Archive-663/nishiKodak/Nikon F DX/README.md

## Lot no. 006 | NishiKodak - for Nikon F DX

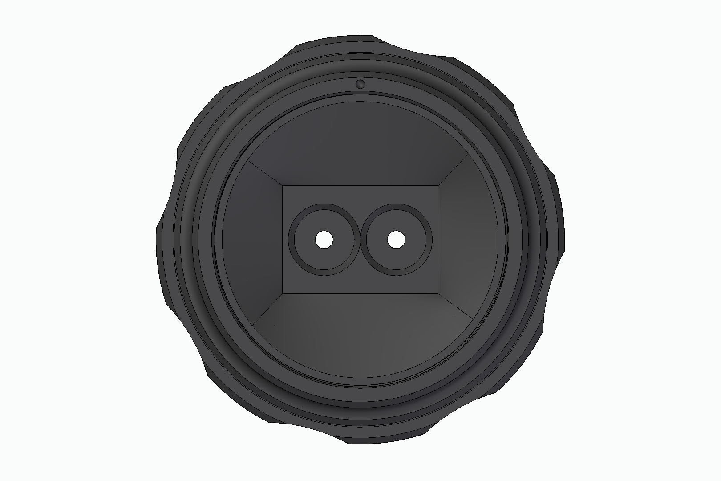
[picture p33: ASSETS/nishiKodak_nikonF_DX.jpg]

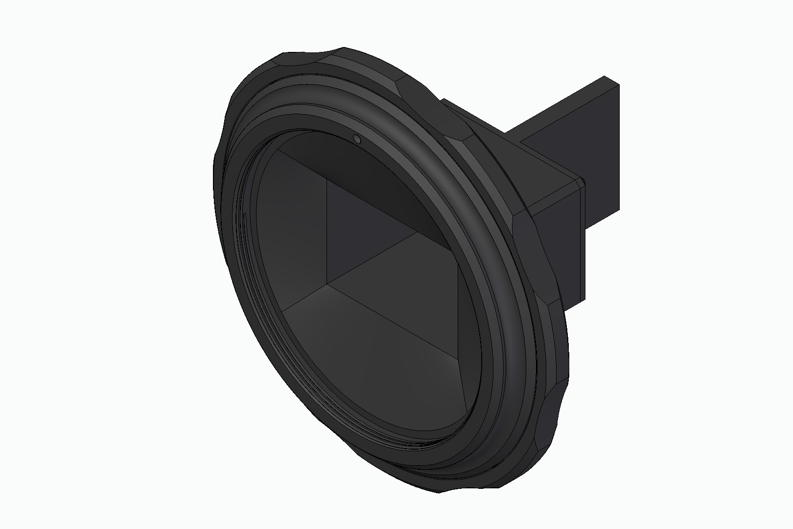
[picture p34: ASSETS/nishiKodak_nikonF_DX-1.jpg]

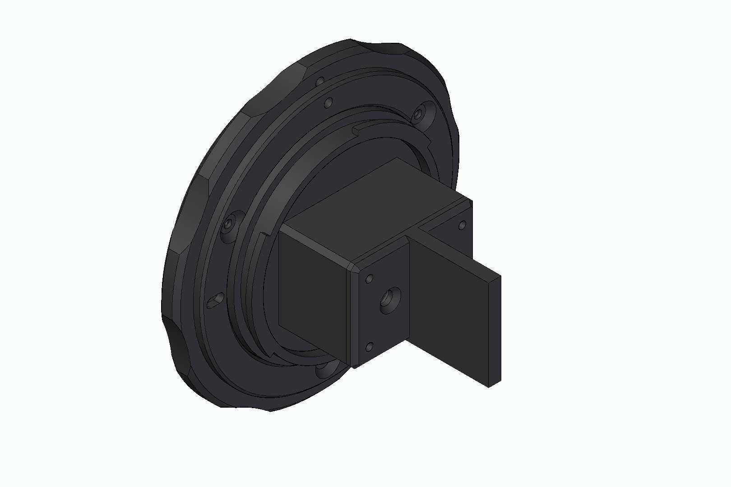
[picture p35: ASSETS/nishiKodak_nikonF_DX-2.jpg]


### Features:
- Breech-lock  mounting ring
- 30mm focal length
- Fixed ~f11 aperture
- Two individual images on one frame

### Compatibility Note:
You need a Nikon body that allows for mirror lock up. Some older film cameras allowed you to hold the mirror up with hardware, but there are some that link the mirror actuation to the shutter actuation so you can't lock your mirror up. Just make sure you have mirror lock up. Tested on a D700 + D200.

### What you'll need:
- Lots of M1.6 x 5mm pan head screws (PETG or ABS filament)
  
  or

- Lots of M1.6 x 5mm self tapping screws (ABS filament)
- 1x M1.6 tap
- 2x Kodak Funsaver lenses (post-2015 expiration date. Kodak had a few lens changes in the Funsaver production lifetime. You'll need a recent Funsaver to make this work)
- <a href="https://github.com/Archive-663/kodakFunsaver/tree/main/DSLRviewFinder/STL">30mm Kodak Funsaver Viewfinder Rehousing</a>

### What would be helpful:
- M1.4 drill bit
- M1.8/M2 drill bit

### Printing help:
I print with PETG because it's pretty easy to set up with and dial in. If you want to use something else, go for it. I'd stay away from PLA because it's not the best in heat and against solvents. 

Generally, my designs have chamfers on the print face of the STL.

Please view the printOrientation.3mf file for help with orienting the parts on the printer bed. 

### Assembly help:
I suggest drilling holds to their correct tap size before tapping. The M1.6 holes should be drilled out to 1.4mm then tapped with the M1.6 tap. 

When assembling the rotating assemblies use some synthetic grease similar to Super Lube PTFE or keycap lube to make the rotate function smoother.

Please view the _assembly.stp file for help in parts orientation. If you do not have a CAD program, <a href="https://www.freecad.org/downloads.php" target="_blank">download FreeCAD</a> to view the assembly file and better understand how it should assemble.

### Samples:

Coming Soon.

### Helpful videos:
- <a href="https://www.youtube.com/watch?v=ZdX-1SL8kYE" target="_blank">Old Print and Assembly Video</a>
- <a href="https://www.youtube.com/watch?v=JzHJL4l5Iv4" target="_blank">How to wigglegram</a>
- <a href="https://www.youtube.com/watch?v=mniP1P2PrpM" target="_blank">Kodak Funsaver Disassembly</a>

### Help support Archive 663 with a dontation or monthly sub
