Archive-663/nishiKodak/Sony E/STL/nishiKodak_sonyE_depthChecker.stl

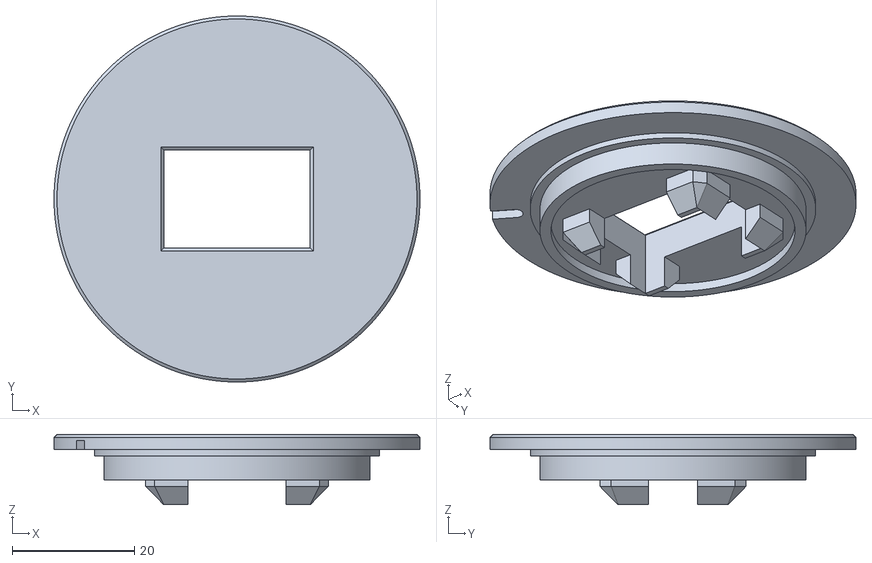
[picture p57: CAD file, 2023-11-09]
Sony E/STL/nishiKodak_sonyE_depthChecker.stl
60.0 x 60.0 x 11.5
