Archive-663/nishiKodak/Sony FE/STL/nishiKodak_sonyFE_depthChecker.stl

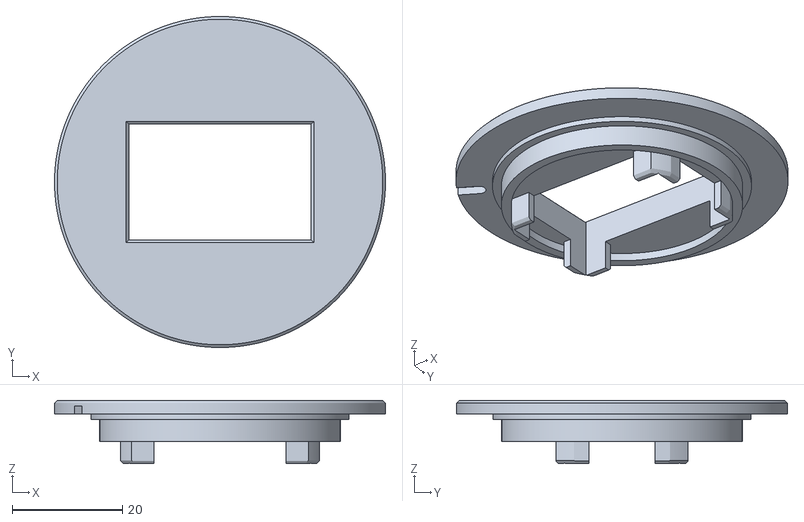
[picture p58: CAD file, 2023-11-09]
Sony FE/STL/nishiKodak_sonyFE_depthChecker.stl
60.0 x 60.0 x 11.5
