Archive-663/nishiKodak/Canon EF-S/STL/nishiKodak_canonEF_rearCap.stl

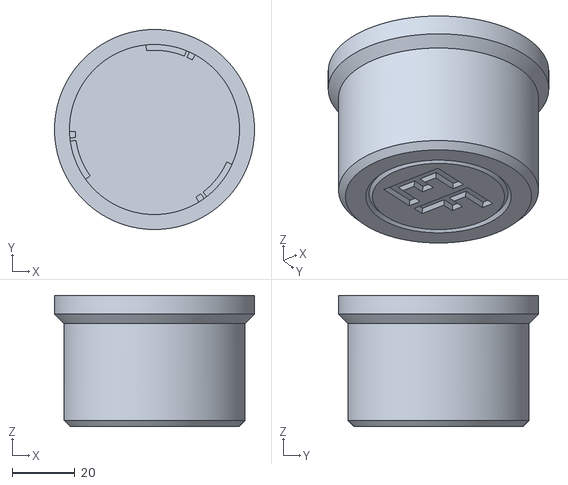
[picture p59: CAD file, 2023-11-06]
Canon EF-S/STL/nishiKodak_canonEF_rearCap.stl
64.0 x 64.0 x 42.0
