Archive-663/nishiKodak/Canon EF/STL/nishiKodak_canonEF_mountLockRing.stl

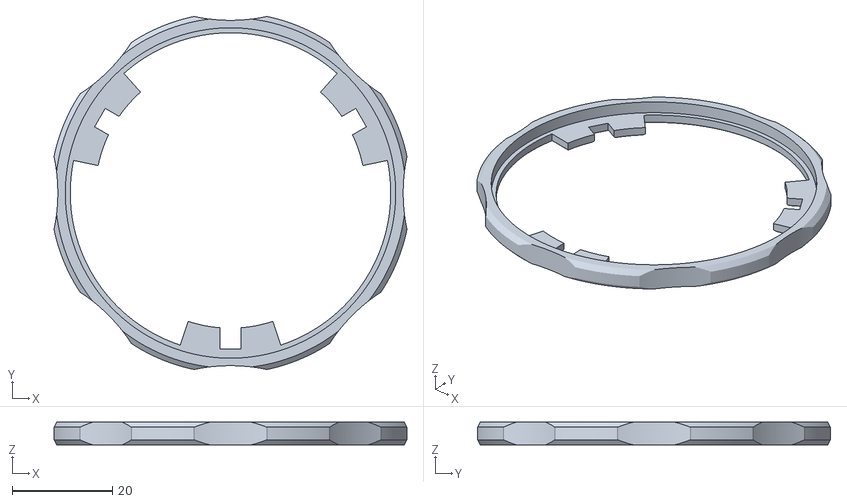
[picture p60: CAD file, 2023-11-06]
Canon EF/STL/nishiKodak_canonEF_mountLockRing.stl
70.5 x 70.5 x 4.50
