Archive-663/nishiKodak/Canon FD/STL/nishiKodak_canonFD_breechLock.stl

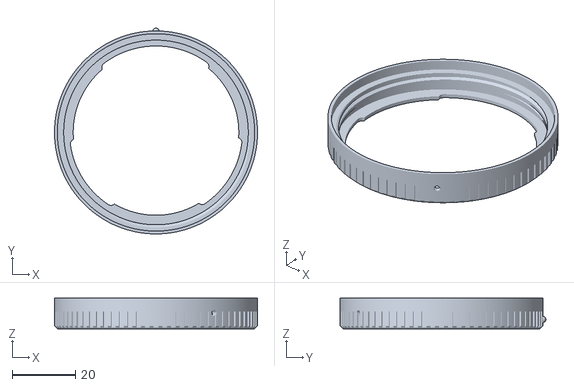
[picture p61: CAD file, 2023-11-06]
Canon FD/STL/nishiKodak_canonFD_breechLock.stl
64.0 x 64.9 x 9.75
