Archive-663/nishiKodak/Canon RF/STL/printOrientation_nishiKodak_canonRF.3mf

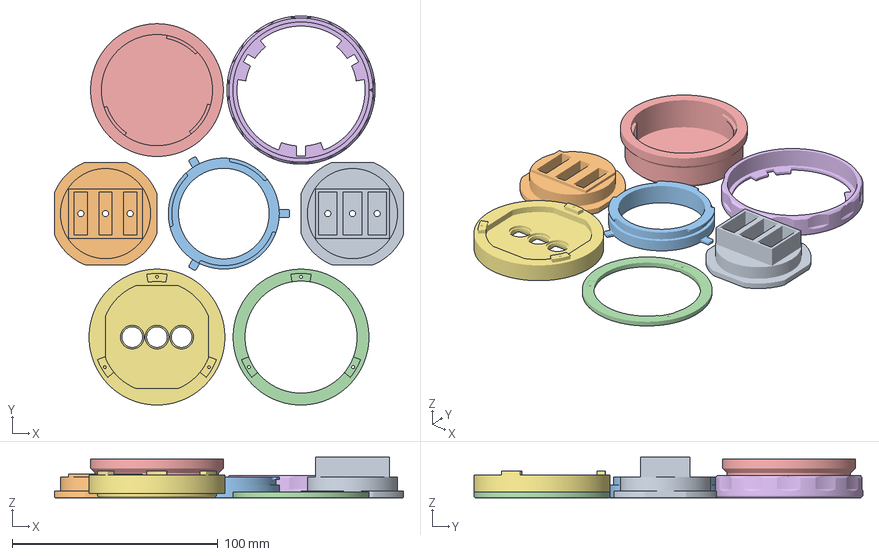
[picture p62: CAD file, 2023-11-07]
Canon RF/STL/printOrientation_nishiKodak_canonRF.3mf
169.8 x 189.0 x 19.8 mm
nishiKodak_canonRF_lensBaffle_long.stl
nishiKodak_canonRF_lensBaffle_short.stl
nishiKodak_canonRF_mountFlange.stl
nishiKodak_canonRF_mountCap.stl
nishiKodak_canonRF_rearCap.stl
nishiKodak_canonRF_mountLockRing.stl
nishiKodak_canonRF_lensBody.stl
