Archive-663/nishiKodak/Fuji GFX/STEP/nishiKodak_GFX_depthChecker.stp

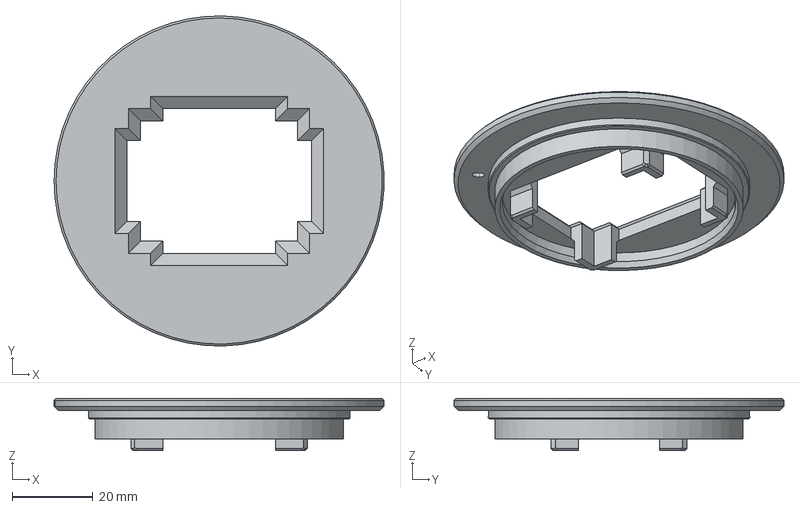
[picture p63: CAD file, 2025-04-08]
Fuji GFX/STEP/nishiKodak_GFX_depthChecker.stp
81.9 x 82.0 x 13.0 mm
