Archive-663/nishiKodak/Fuji GFX/STL/mountRearCapGFX.stl

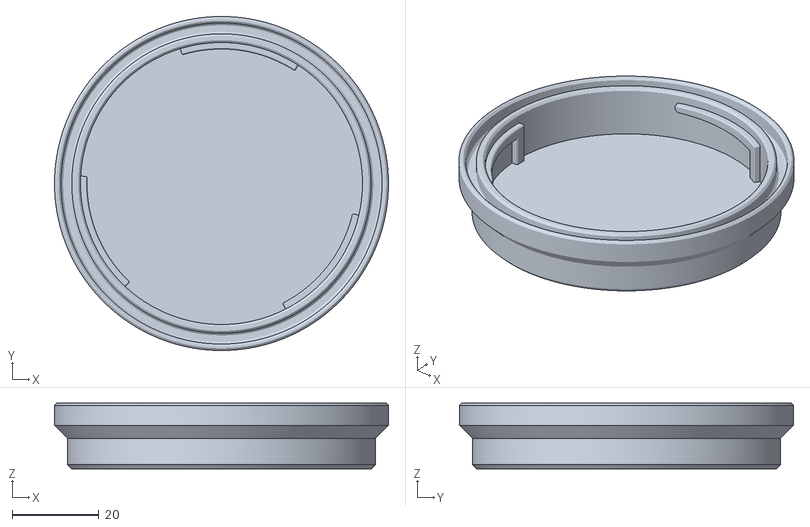
[picture p64: CAD file, 2025-04-08]
Fuji GFX/STL/mountRearCapGFX.stl
77.0 x 77.0 x 15.1
