Archive-663/nishiKodak/Fuji X/STL/nishiKodak_fujiX_depthChecker.stl

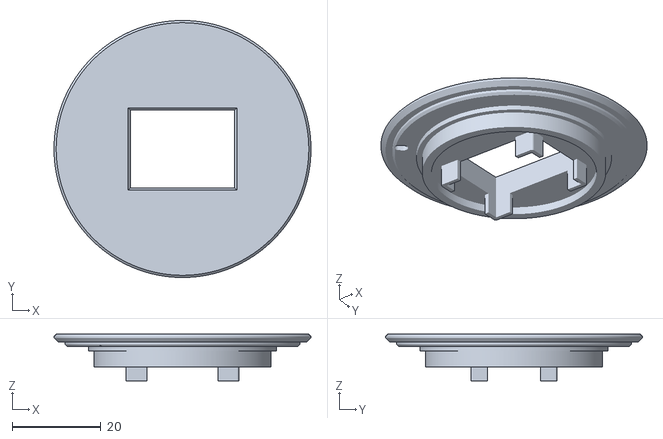
[picture p65: CAD file, 2023-11-09]
Fuji X/STL/nishiKodak_fujiX_depthChecker.stl
58.0 x 58.0 x 10.5
