Archive-663/nishiKodak/Leica M/STL/printOrientation_nishiKodak_leicaM.3mf

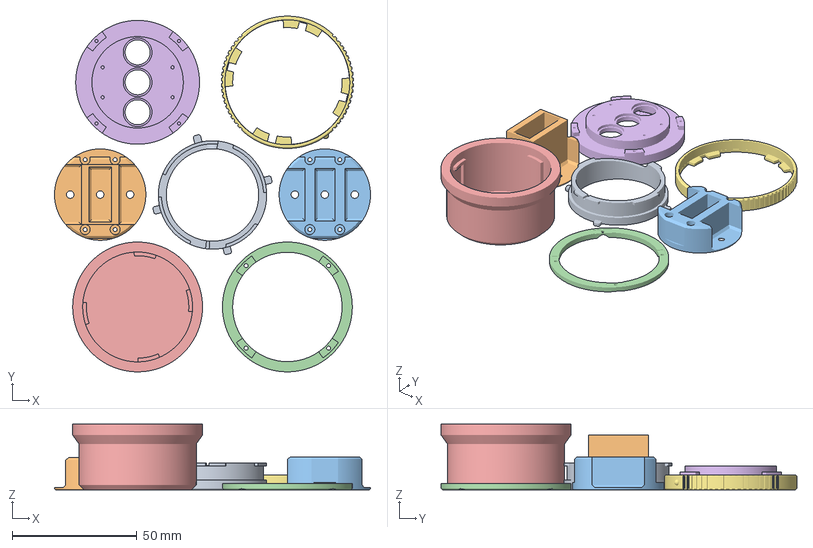
[picture p66: CAD file, 2023-11-07]
Leica M/STL/printOrientation_nishiKodak_leicaM.3mf
126.6 x 142.5 x 26.3 mm
nishiKodak_leicaM_mountFlange.stl
nishiKodak_leicaM_lensBaffle_long.stl
nishiKodak_leicaM_lensBaffle_short.stl
nishiKodak_leicaM_mountCap.stl
nishiKodak_leicaM_rearCap.stl
nishiKodak_leicaM_lensBody.stl
nishiKodak_leicaM_mountLockRing.stl
