Archive-663/nishiKodak/M42/STL/nishiKodak_M42_lensBody.stl

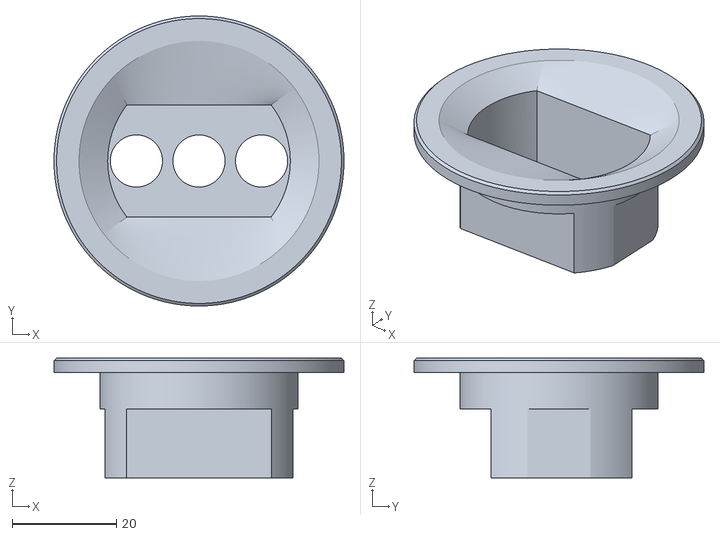
[picture p67: CAD file, 2023-11-06]
M42/STL/nishiKodak_M42_lensBody.stl
55.6 x 55.6 x 23.0
