Archive-663/nishiKodak/Nikon F DX/STL/nishiKodak_nikonF-FX_mountCap.stl

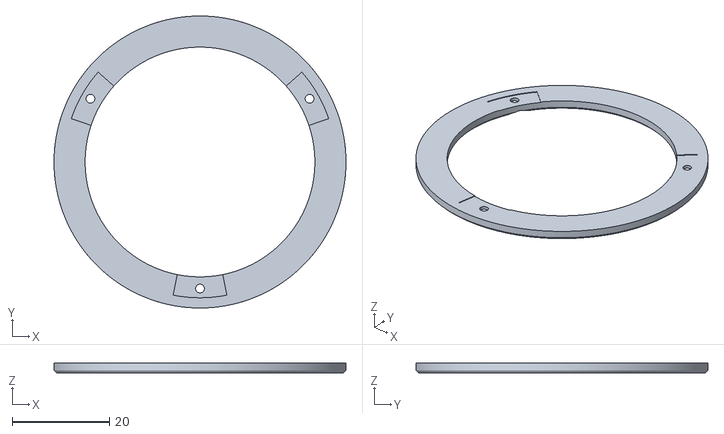
[picture p68: CAD file, 2023-11-07]
Nikon F DX/STL/nishiKodak_nikonF-FX_mountCap.stl
60.0 x 60.0 x 2.00
