Archive-663/nishiKodak/Nikon Z FX/STL/printOrientation_nishiKodak_nikonZ.3mf

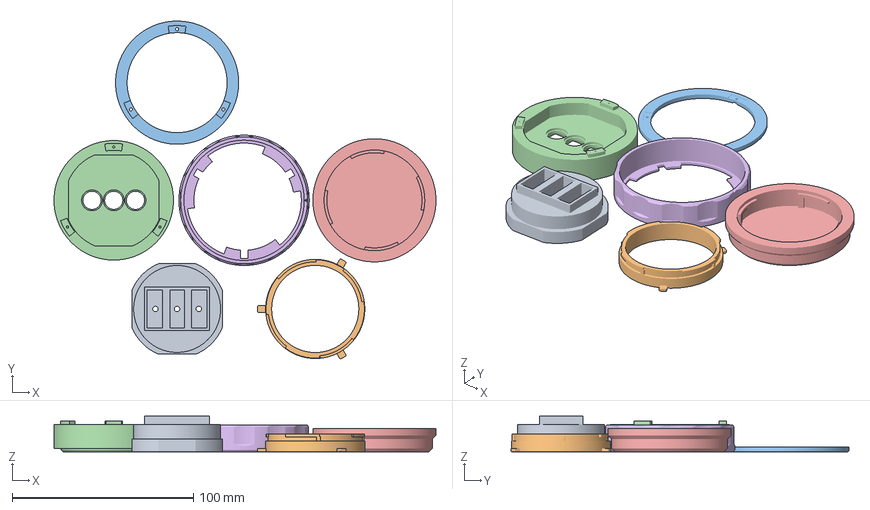
[picture p69: CAD file, 2023-11-07]
Nikon Z FX/STL/printOrientation_nishiKodak_nikonZ.3mf
211.0 x 186.6 x 19.8 mm
nishiKodak_nikonZ_lensBaffle.stl
nishiKodak_nikonZ_mountFlange.stl
nishiKodak_nikonZ_mountCap.stl
nishiKodak_nikonZ_lensBody.stl
nishiKodak_nikonZ_rearCap.stl
nishiKodak_nikonZ_mountLockRing.stl
