Archive-663/nishiKodak/Sony E/STL/printOrientation_nishiKodak_sonyE.3mf

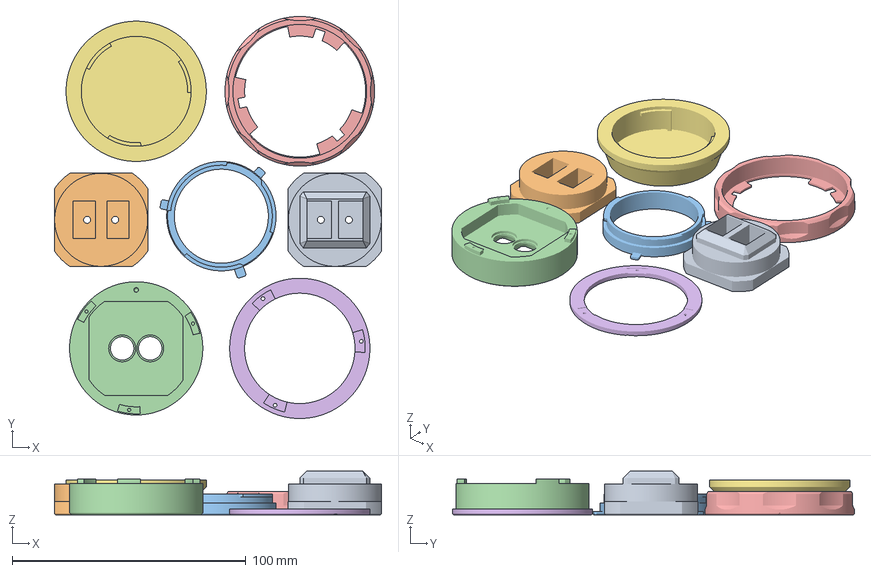
[picture p70: CAD file, 2023-11-07]
Sony E/STL/printOrientation_nishiKodak_sonyE.3mf
140.0 x 172.0 x 18.8 mm
nishiKodak_sonyE_lensBaffle_long.stl
nishiKodak_sonyE_lensBaffle_short.stl
nishiKodak_sonyFE_mountFlange.stl
nishiKodak_sonyE_lensBody.stl
nishiKodak_sonyFE_mountLockRing.stl
nishiKodak_sonyFE_mountCap.stl
nishiKodak_sonyFE_rearCap.stl
