Archive-663/nishiKodak/Sony FE/STL/printOrientation_nishiKodak_sonyFE.3mf

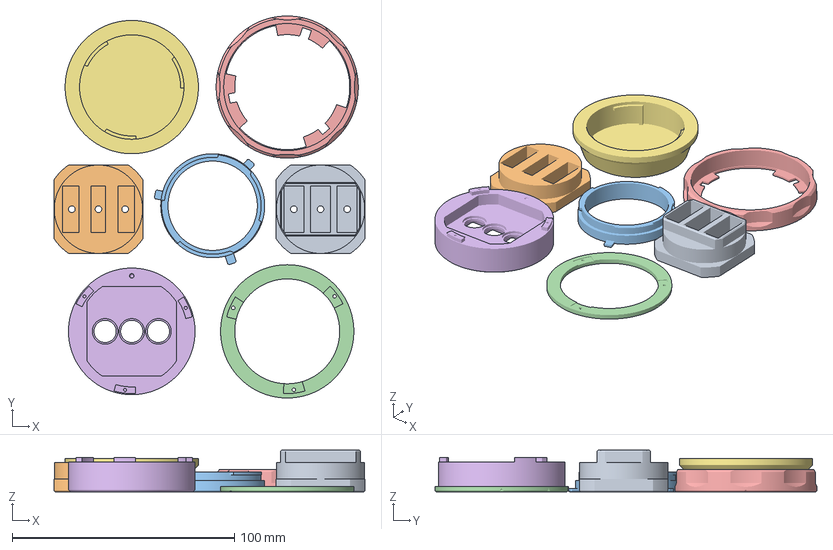
[picture p71: CAD file, 2023-11-07]
Sony FE/STL/printOrientation_nishiKodak_sonyFE.3mf
140.0 x 172.0 x 18.8 mm
nishiKodak_sonyFE_lensBaffle_long.stl
nishiKodak_sonyFE_lensBaffle_short.stl
nishiKodak_sonyFE_mountFlange.stl
nishiKodak_sonyFE_mountCap.stl
nishiKodak_sonyFE_mountLockRing.stl
nishiKodak_sonyFE_lensBody.stl
nishiKodak_sonyFE_rearCap.stl
