Archive-663/nishiKodak/Canon EF-S/STL/nishiKodak_canonEF-S_lensBaffle-4_5mm.stl

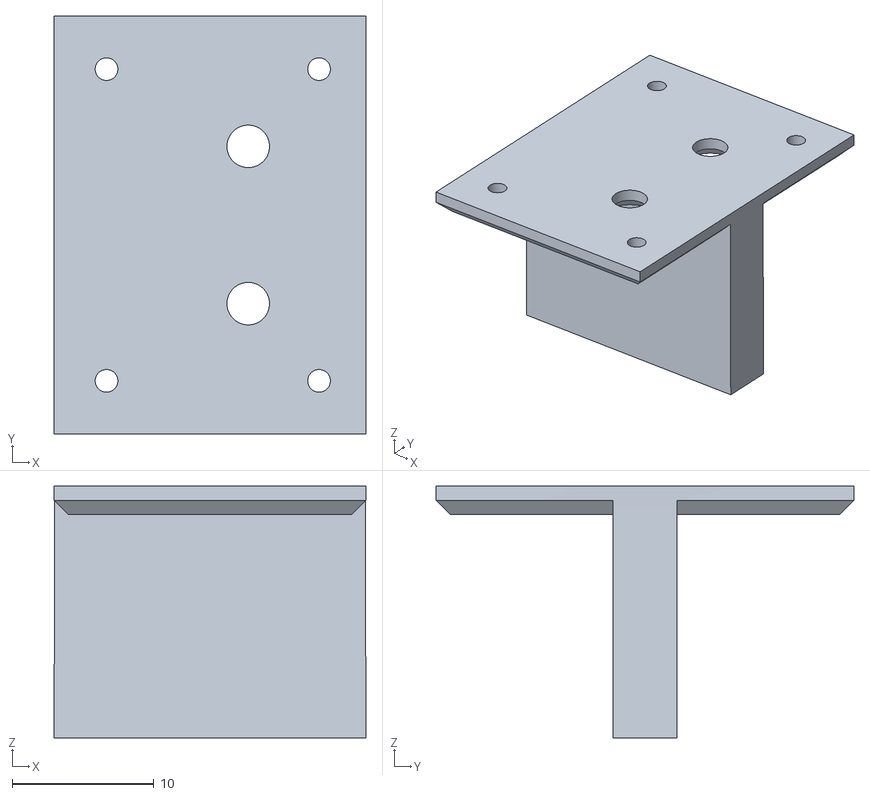
[picture p72: CAD file, 2023-11-06]
Canon EF-S/STL/nishiKodak_canonEF-S_lensBaffle-4_5mm.stl
22.0 x 29.5 x 17.8
