Archive-663/nishiKodak/Canon EF/STL/nishiKodak_canonEF_mountFlange.stl

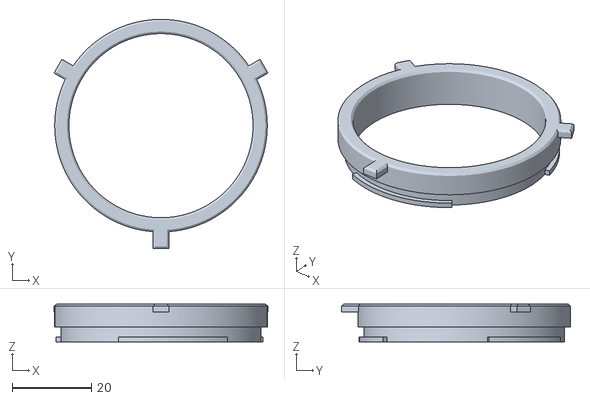
[picture p73: CAD file, 2023-11-06]
Canon EF/STL/nishiKodak_canonEF_mountFlange.stl
54.0 x 57.8 x 9.50
