Archive-663/nishiKodak/Canon FD/STL/nishiKodak_canonFD_rearCap.stl

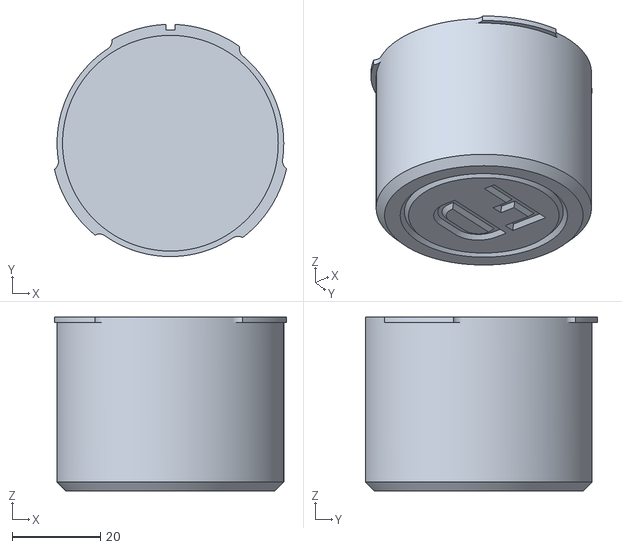
[picture p74: CAD file, 2023-11-06]
Canon FD/STL/nishiKodak_canonFD_rearCap.stl
52.7 x 52.7 x 39.5
