Archive-663/nishiKodak/Canon RF/STL/nishiKodak_canonRF_lensBody.stl

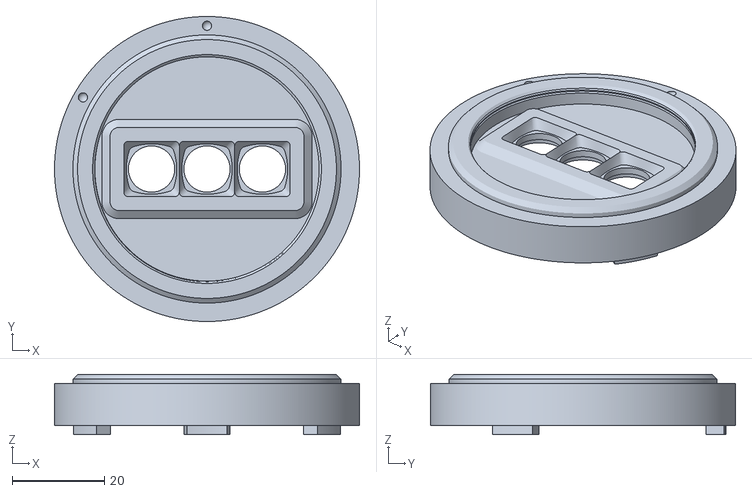
[picture p75: CAD file, 2023-11-06]
Canon RF/STL/nishiKodak_canonRF_lensBody.stl
66.0 x 66.0 x 13.0
