Archive-663/nishiKodak/Fuji GFX/STL/nishiKodak_GFX_lensBaffle_short.stl

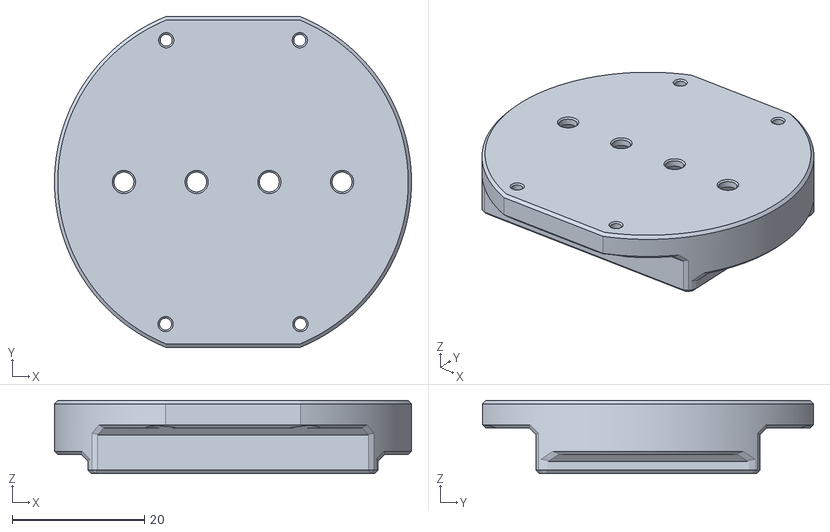
[picture p76: CAD file, 2025-04-08]
Fuji GFX/STL/nishiKodak_GFX_lensBaffle_short.stl
54.0 x 50.0 x 11.1
