Archive-663/nishiKodak/Fuji X/STL/printOrientation_nishiKodak_fujiX.3mf

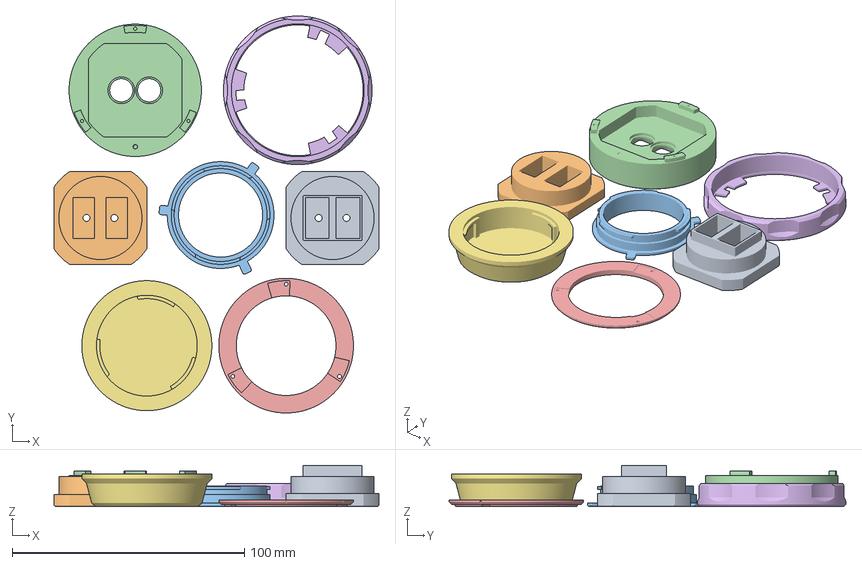
[picture p77: CAD file, 2023-11-07]
Fuji X/STL/printOrientation_nishiKodak_fujiX.3mf
140.0 x 171.0 x 17.8 mm
nishiKodak_fujiX_lensBaffle_long.stl
nishiKodak_fujiX_lensBaffle_short.stl
nishiKodak_fujiX_mountFlange.stl
nishiKodak_fujiX_lensBody.stl
nishiKodak_fujiX_mountCap.stl
nishiKodak_fujiX_mountLockRing.stl
nishiKodak_fujiX_rearCap.stl
