Archive-663/nishiKodak/Leica M/STL/nishiKodak_leicaM_lensBody.stl

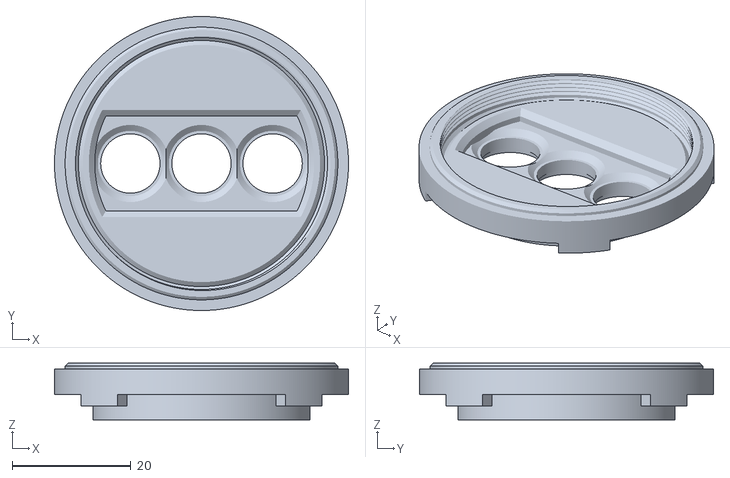
[picture p78: CAD file, 2023-11-07]
Leica M/STL/nishiKodak_leicaM_lensBody.stl
49.6 x 49.6 x 9.55
