Archive-663/nishiKodak/M42/STL/nishiKodak_M42_lensFace.stl

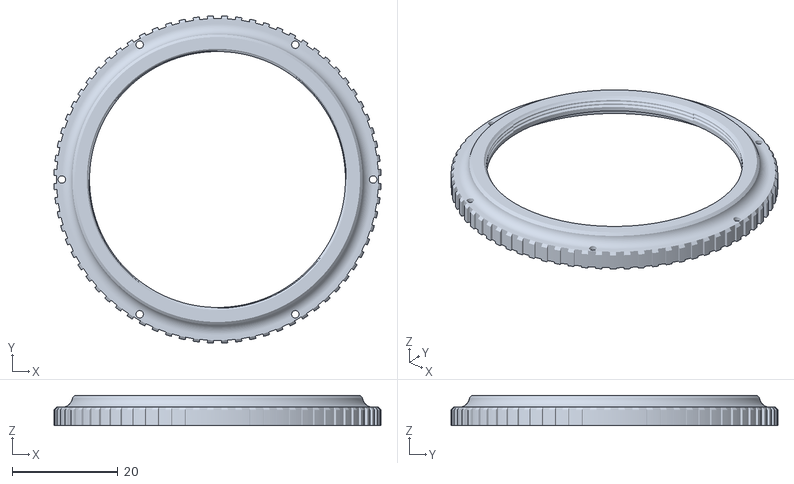
[picture p79: CAD file, 2023-11-06]
M42/STL/nishiKodak_M42_lensFace.stl
62.0 x 62.0 x 5.75
