Archive-663/nishiKodak/Nikon F DX/STL/nishiKodak_nikonF-DX_lensBaffle.stl

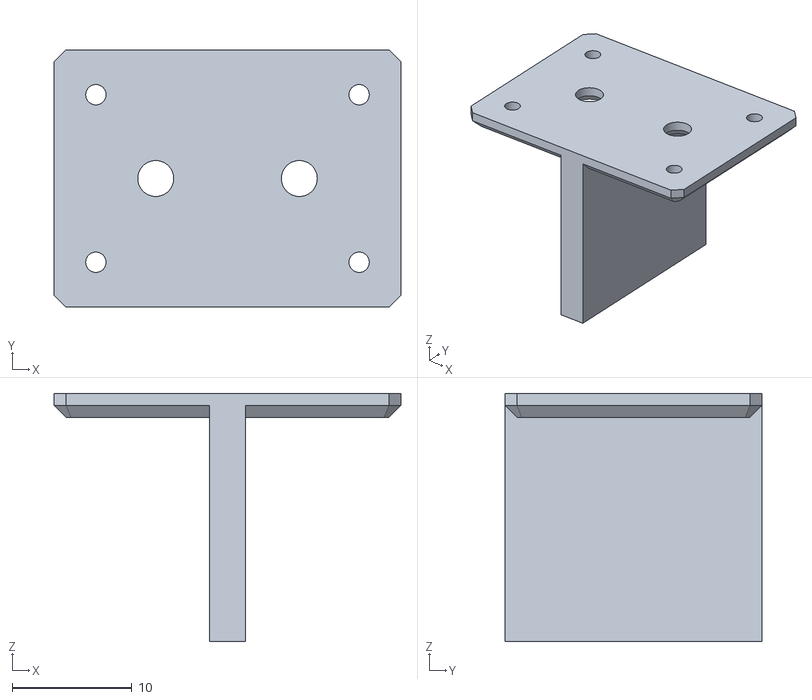
[picture p80: CAD file, 2023-11-06]
Nikon F DX/STL/nishiKodak_nikonF-DX_lensBaffle.stl
29.0 x 21.5 x 20.8
