Archive-663/nishiKodak/Nikon F FX/STL/nishiKodak_nikonF-FX_mountFlange.stl

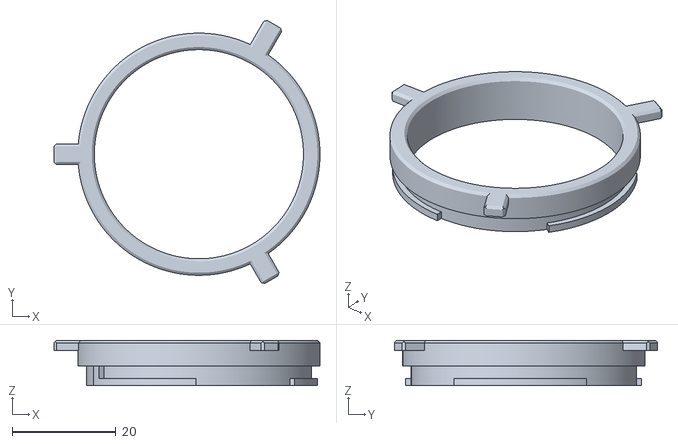
[picture p81: CAD file, 2023-11-06]
Nikon F FX/STL/nishiKodak_nikonF-FX_mountFlange.stl
51.4 x 50.9 x 8.75
