Archive-663/nishiKodak/Nikon Z FX/STL/nishiKodak_nikonZ_mountFlange.stl

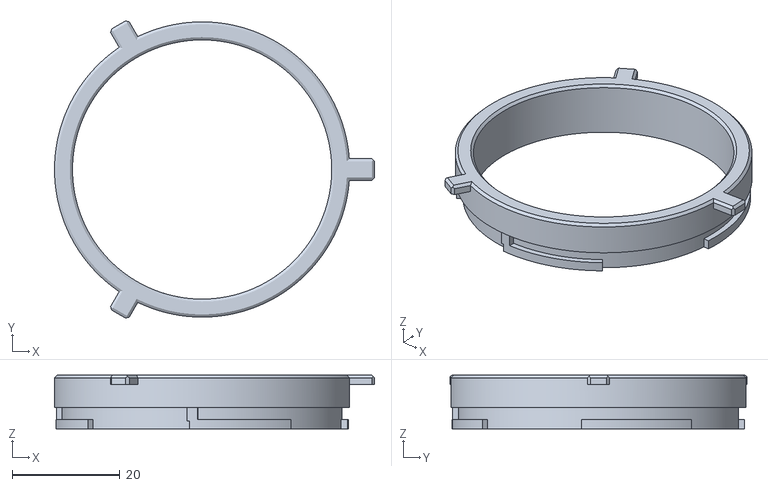
[picture p82: CAD file, 2023-11-06]
Nikon Z FX/STL/nishiKodak_nikonZ_mountFlange.stl
59.4 x 55.2 x 10.0
