Archive-663/nishiKodak/Sony E/STL/nishiKodak_sonyE_lensBody.stl

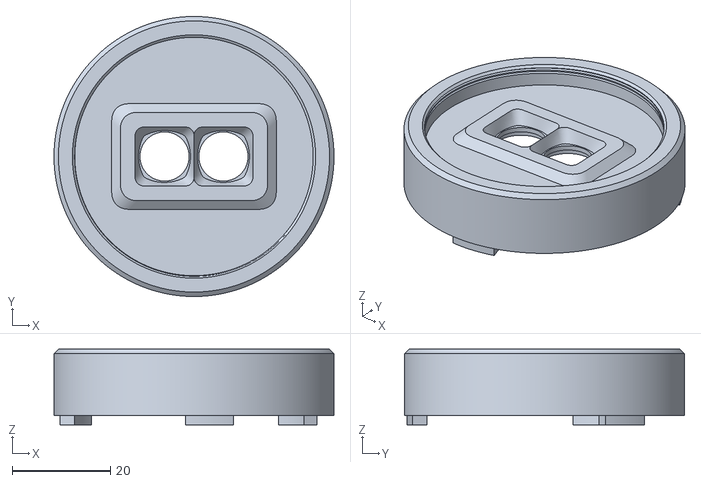
[picture p83: CAD file, 2023-11-06]
Sony E/STL/nishiKodak_sonyE_lensBody.stl
57.0 x 57.0 x 15.4
