Archive-663/nishiKodak/Sony FE/STL/nishiKodak_sonyFE_lensBaffle_long.stl

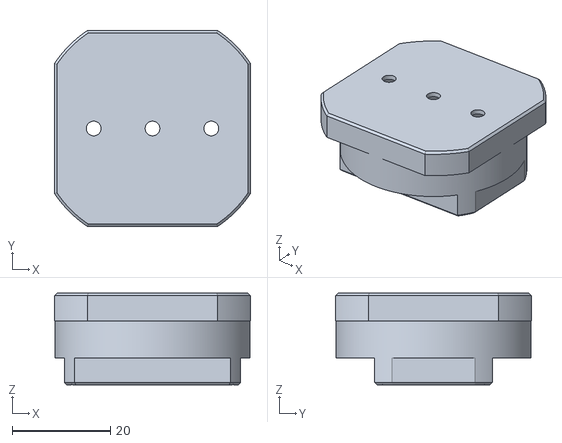
[picture p84: CAD file, 2023-11-06]
Sony FE/STL/nishiKodak_sonyFE_lensBaffle_long.stl
40.0 x 40.0 x 18.8
