Archive-663/nishiKodak/Canon RF/STL/nishiKodak_canonRF_rearCap.stl

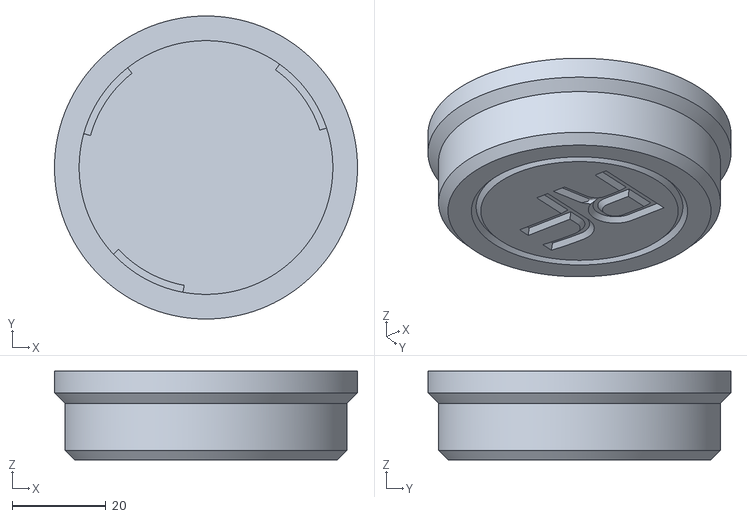
[picture p85: CAD file, 2023-11-06]
Canon RF/STL/nishiKodak_canonRF_rearCap.stl
64.5 x 64.5 x 18.9
