Archive-663/nishiKodak/Fuji X/STL/nishiKodak_fujiX_mountLockRing.stl

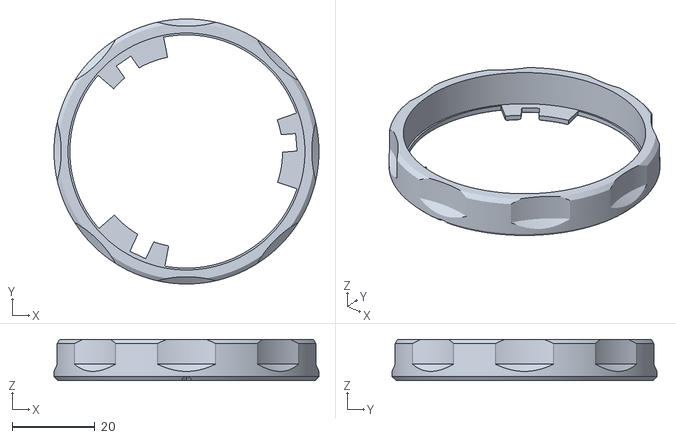
[picture p86: CAD file, 2023-11-07]
Fuji X/STL/nishiKodak_fujiX_mountLockRing.stl
64.0 x 64.0 x 10.0
