Archive-663/nishiKodak/Leica M/STL/nishiKodak_leicaM_rearCap.stl

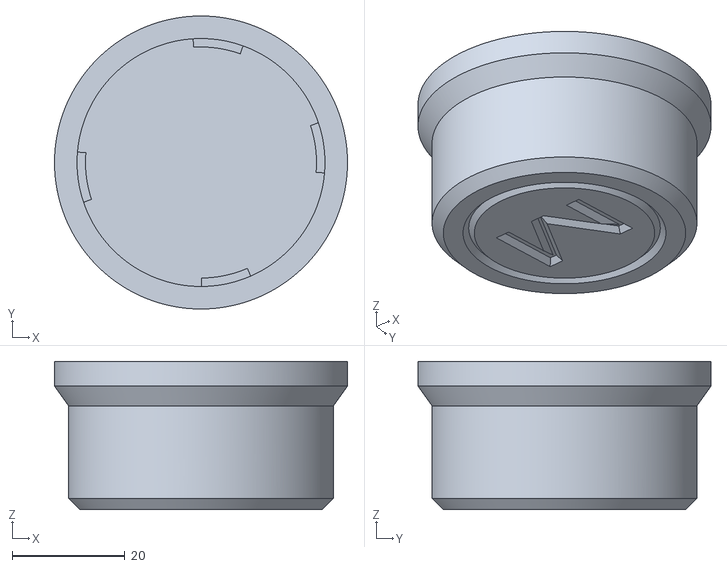
[picture p87: CAD file, 2023-11-06]
Leica M/STL/nishiKodak_leicaM_rearCap.stl
52.0 x 52.0 x 26.3
