Archive-663/nishiKodak/M42/STL/nishiKodak_M42_lensBaffle.stl

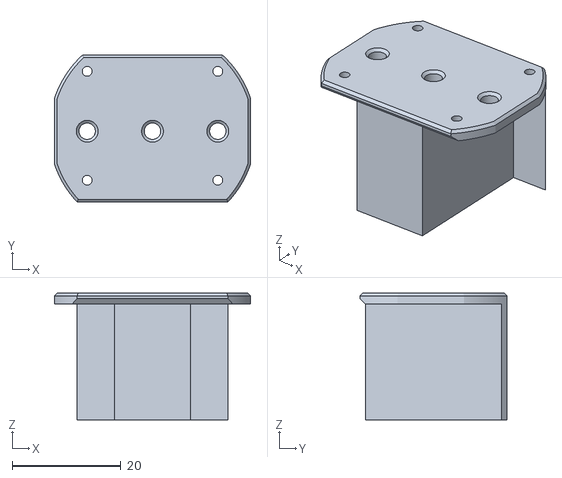
[picture p88: CAD file, 2023-11-06]
M42/STL/nishiKodak_M42_lensBaffle.stl
36.0 x 27.0 x 23.3
