Archive-663/nishiKodak/Nikon F FX/STL/nishiKodak_nikonF-FX_rearCap.stl

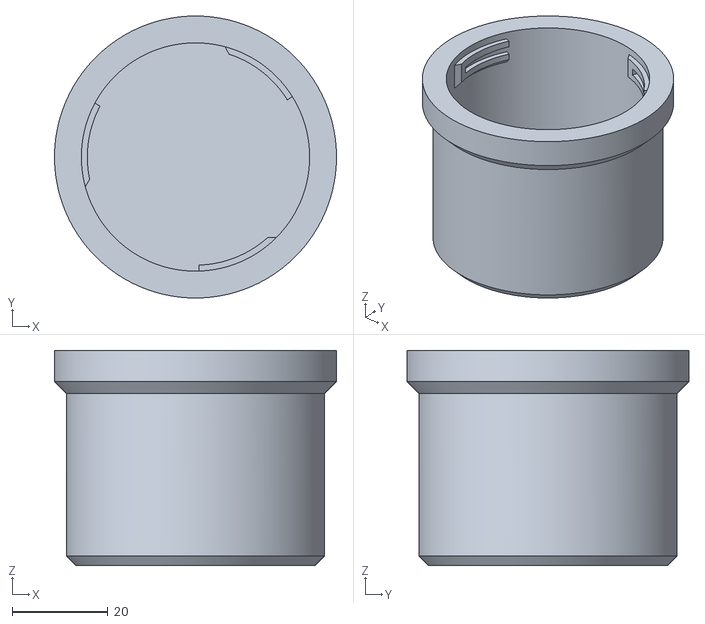
[picture p89: CAD file, 2023-11-06]
Nikon F FX/STL/nishiKodak_nikonF-FX_rearCap.stl
59.0 x 59.0 x 45.0
