Archive-663/nishiKodak/Nikon Z FX/STL/nishiKodak_nikonZ_mountCap.stl

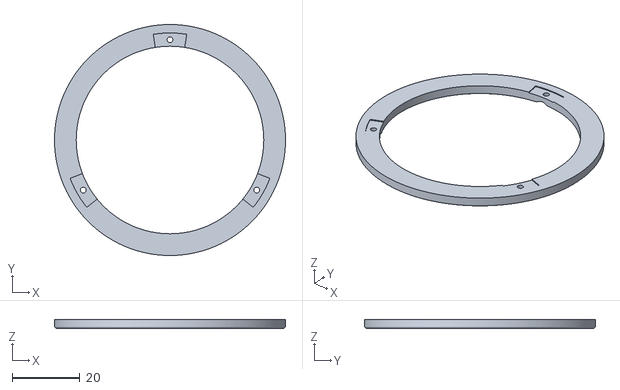
[picture p90: CAD file, 2023-11-06]
Nikon Z FX/STL/nishiKodak_nikonZ_mountCap.stl
68.0 x 68.0 x 2.75
