Archive-663/nishiKodak/Sony E/STL/nishiKodak_sonyFE_mountCap.stl

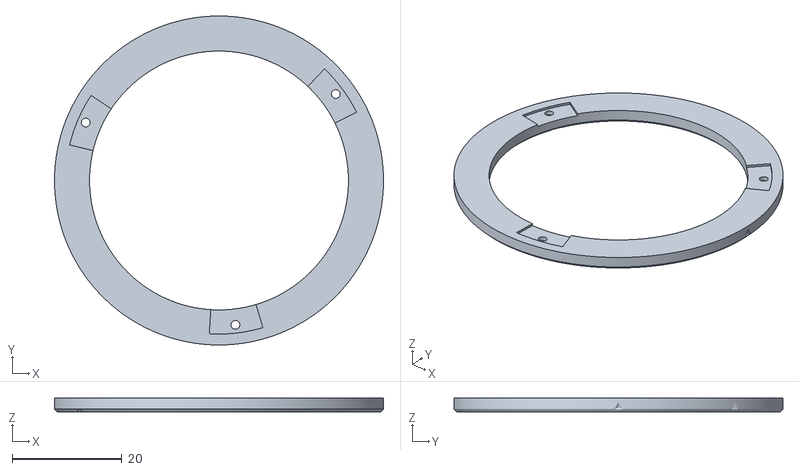
[picture p91: CAD file, 2023-11-06]
Sony E/STL/nishiKodak_sonyFE_mountCap.stl
60.0 x 60.0 x 2.50
