Archive-663/nishiKodak/Sony FE/STL/nishiKodak_sonyFE_lensBody.stl

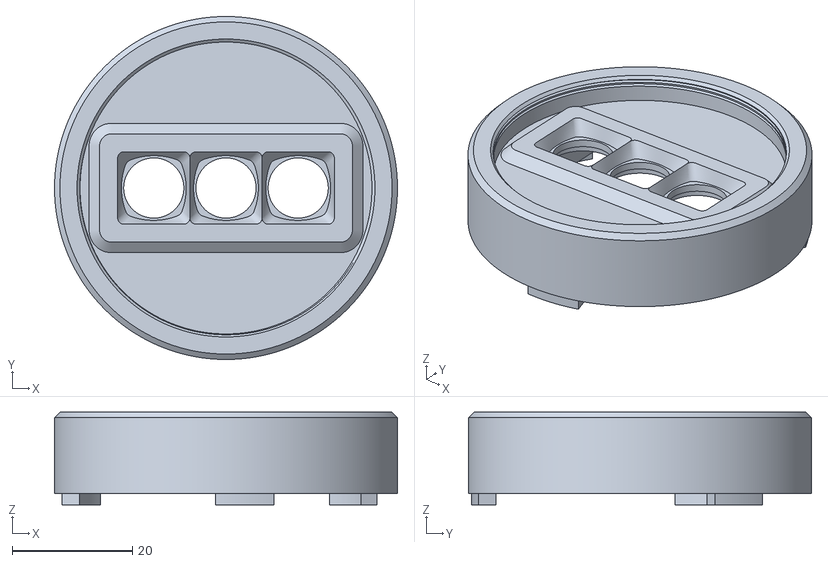
[picture p92: CAD file, 2023-11-06]
Sony FE/STL/nishiKodak_sonyFE_lensBody.stl
57.0 x 57.0 x 15.4
