Archive-663/nishiKodak/Canon EF/STL/nishiKodak_canonEF_lensBaffle.stl

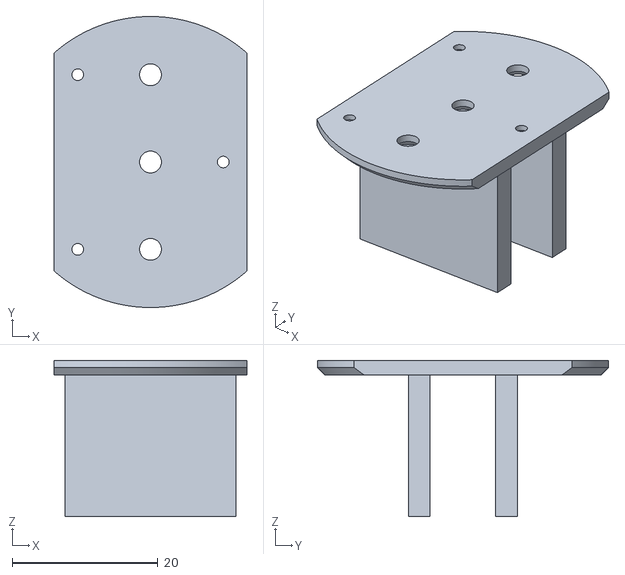
[picture p93: CAD file, 2023-11-06]
Canon EF/STL/nishiKodak_canonEF_lensBaffle.stl
26.5 x 40.0 x 21.5
