Archive-663/nishiKodak/Canon RF/STL/nishiKodak_canonRF_lensBaffle_short.stl

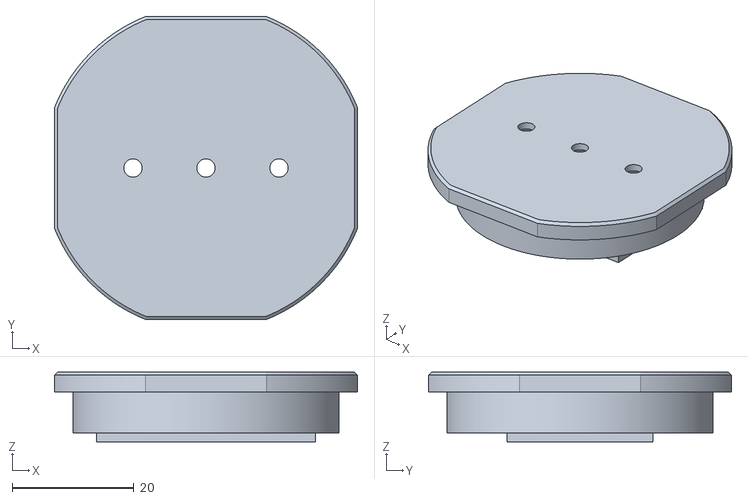
[picture p94: CAD file, 2023-11-06]
Canon RF/STL/nishiKodak_canonRF_lensBaffle_short.stl
49.8 x 49.8 x 11.5
