Archive-663/nishiKodak/Leica M/STL/nishiKodak_leicaM_lensBaffle_long.stl

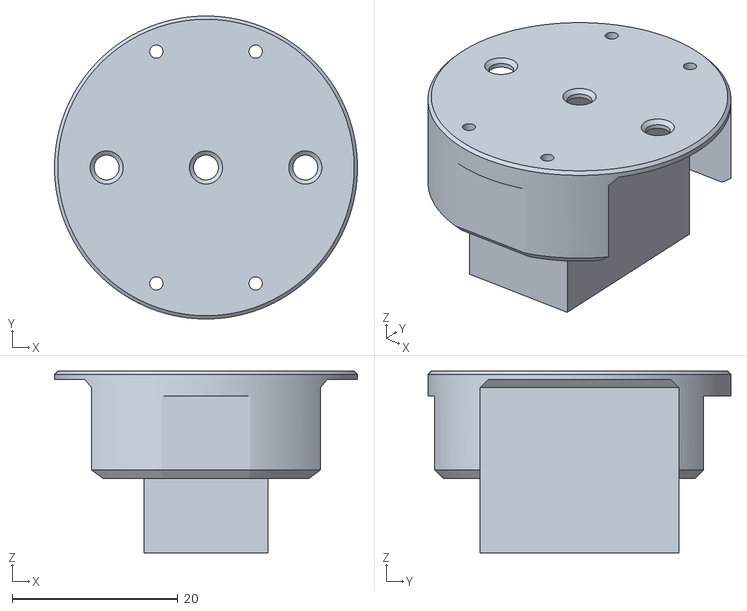
[picture p95: CAD file, 2023-11-06]
Leica M/STL/nishiKodak_leicaM_lensBaffle_long.stl
36.6 x 36.6 x 22.0
