Archive-663/nishiKodak/M42/STL/nishiKodak_M42_mountThreads.stl

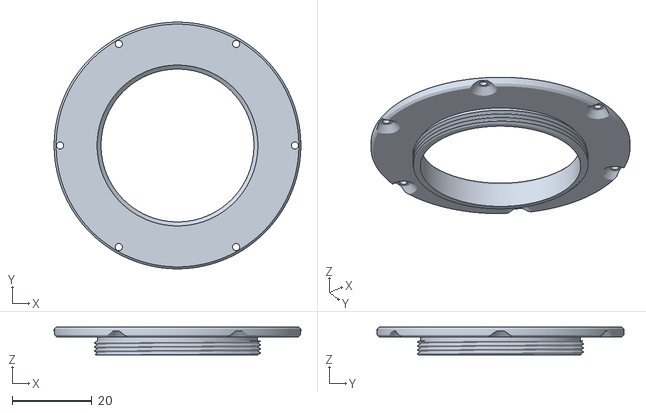
[picture p96: CAD file, 2023-11-06]
M42/STL/nishiKodak_M42_mountThreads.stl
62.1 x 62.0 x 7.00
