Archive-663/nishiKodak/Nikon F FX/STL/nishiKodak_nikonF-FX_mountLockRing.stl

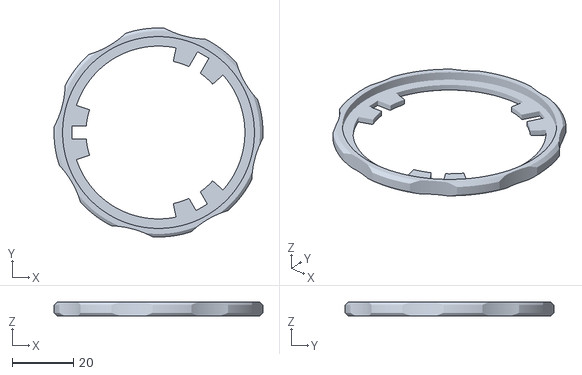
[picture p97: CAD file, 2023-11-06]
Nikon F FX/STL/nishiKodak_nikonF-FX_mountLockRing.stl
68.0 x 68.0 x 4.50
