Archive-663/nishiKodak/Nikon Z FX/STL/nishiKodak_nikonZ_lensBaffle.stl

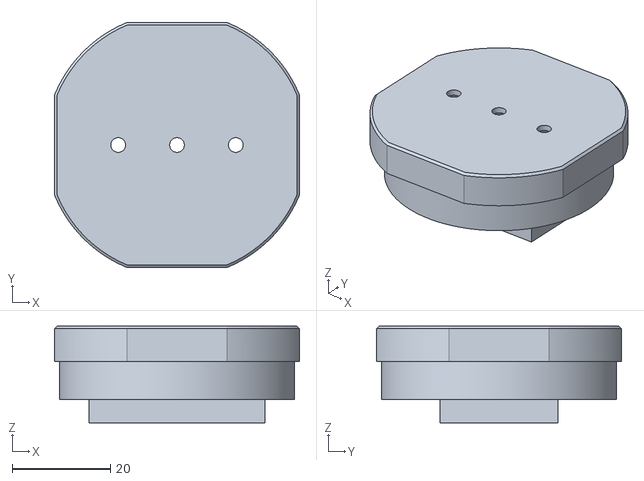
[picture p98: CAD file, 2023-11-06]
Nikon Z FX/STL/nishiKodak_nikonZ_lensBaffle.stl
50.0 x 50.0 x 19.8
