Archive-663/nishiKodak/Sony E/STL/nishiKodak_sonyE_lensBaffle_long.stl

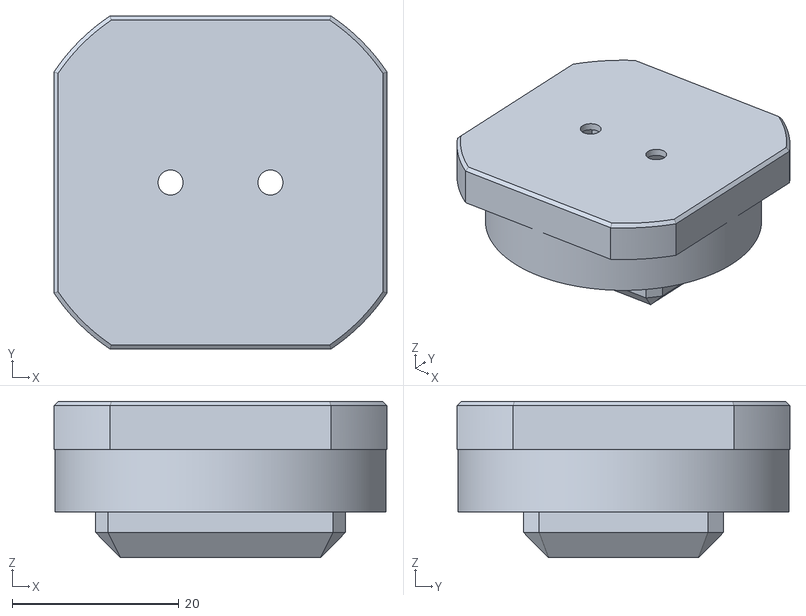
[picture p99: CAD file, 2023-11-06]
Sony E/STL/nishiKodak_sonyE_lensBaffle_long.stl
40.0 x 40.0 x 18.8
