Archive-663/nishiKodak/Canon EF/STL/nishiKodak_canonEF_mountCap.stl

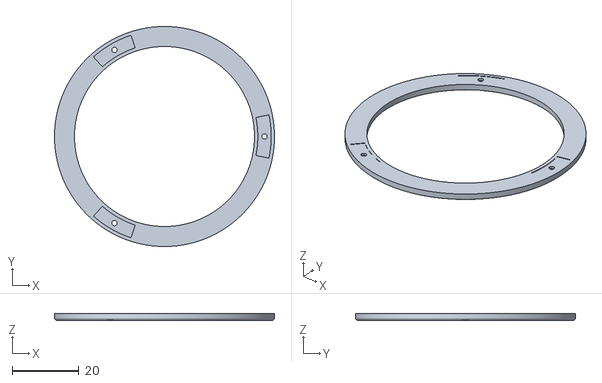
[picture p100: CAD file, 2023-11-06]
Canon EF/STL/nishiKodak_canonEF_mountCap.stl
66.0 x 66.0 x 2.00
