Archive-663/nishiKodak/Canon RF/STL/nishiKodak_canonRF_mountLockRing.stl

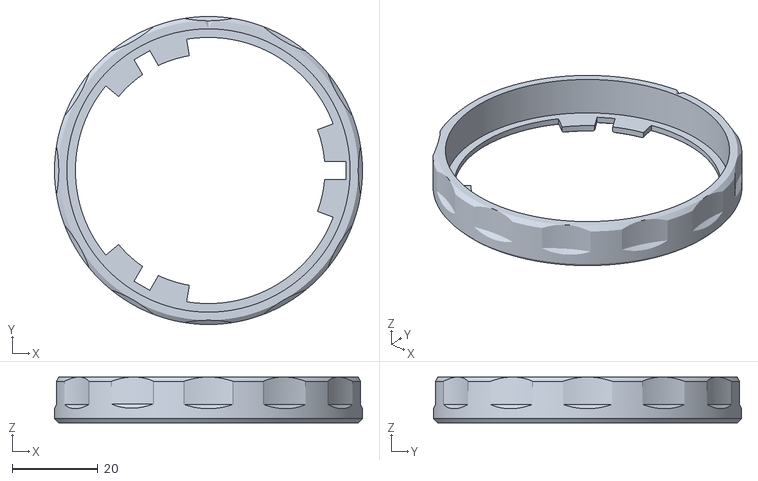
[picture p101: CAD file, 2023-11-06]
Canon RF/STL/nishiKodak_canonRF_mountLockRing.stl
72.0 x 72.0 x 10.8
