Archive-663/nishiKodak/Fuji X/STL/nishiKodak_fujiX_mountFlange.stl

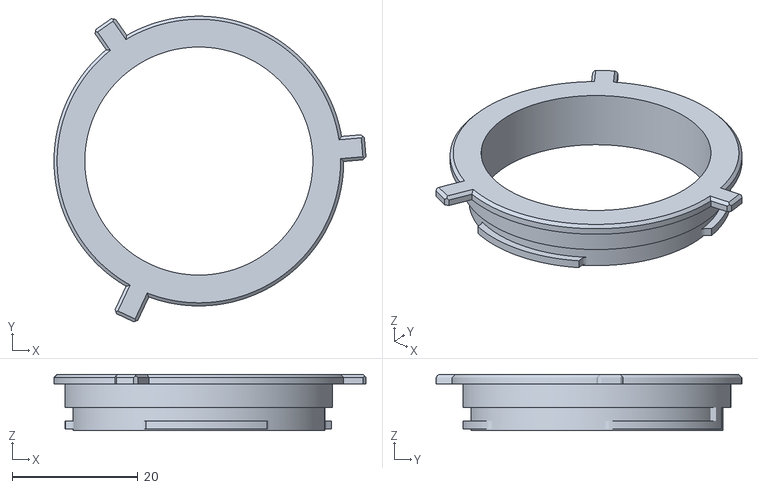
[picture p102: CAD file, 2023-11-06]
Fuji X/STL/nishiKodak_fujiX_mountFlange.stl
49.5 x 48.5 x 8.95
