Archive-663/nishiKodak/Leica M/STL/nishiKodak_leicaM_mountLockRing.stl

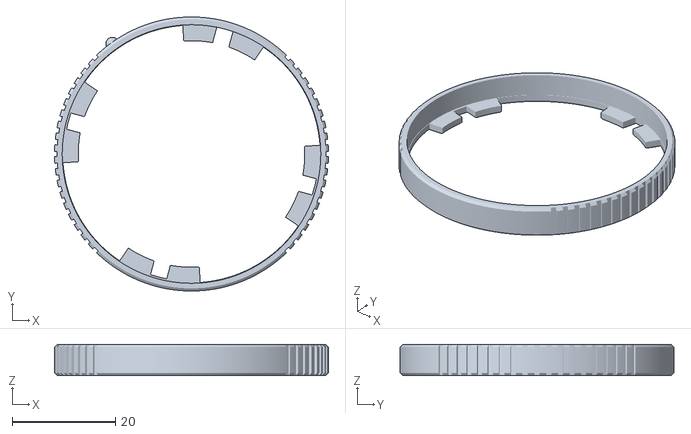
[picture p103: CAD file, 2023-11-06]
Leica M/STL/nishiKodak_leicaM_mountLockRing.stl
53.0 x 53.0 x 6.00
