Archive-663/nishiKodak/Nikon Z FX/STL/nishiKodak_nikonZ_rearCap.stl

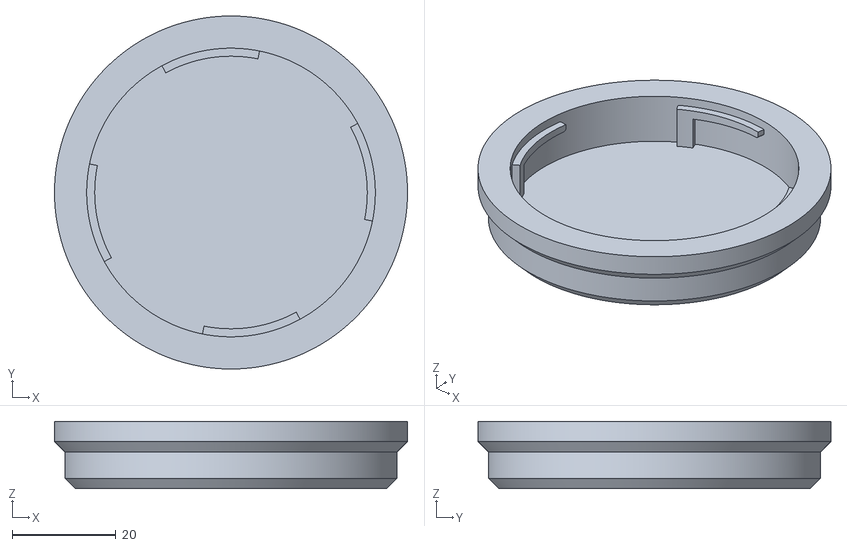
[picture p104: CAD file, 2023-11-06]
Nikon Z FX/STL/nishiKodak_nikonZ_rearCap.stl
68.0 x 68.0 x 13.0
