Archive-663/nishiKodak/Sony E/STL/nishiKodak_sonyFE_rearCap.stl

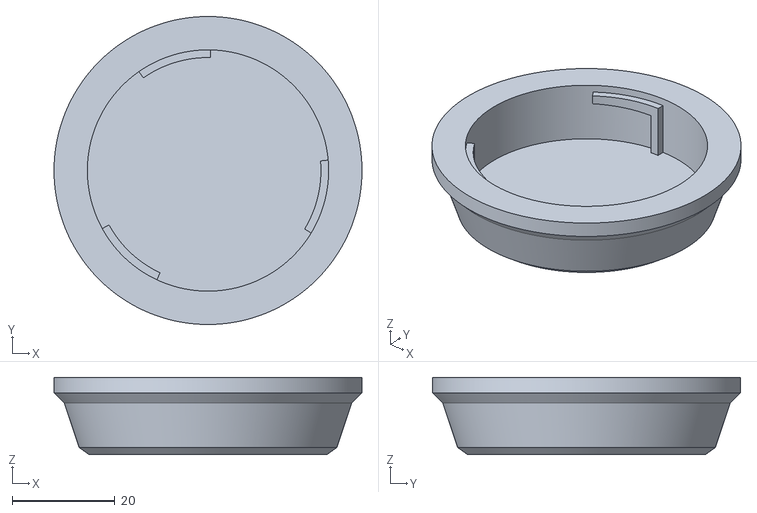
[picture p105: CAD file, 2023-11-06]
Sony E/STL/nishiKodak_sonyFE_rearCap.stl
60.0 x 60.0 x 15.0
