Archive-663/nishiKodak/Sony FE/STL/nishiKodak_sonyFE_lensBaffle_short.stl

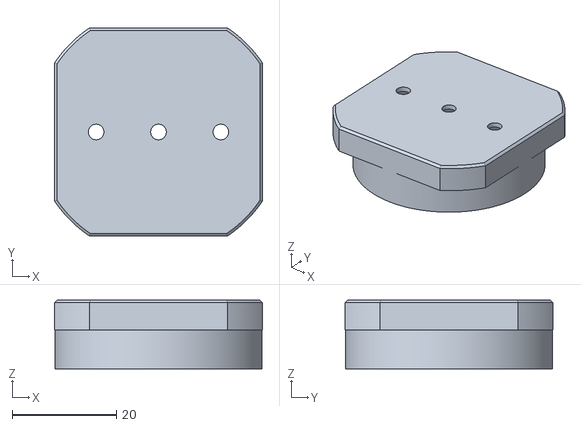
[picture p106: CAD file, 2023-11-06]
Sony FE/STL/nishiKodak_sonyFE_lensBaffle_short.stl
40.0 x 40.0 x 13.3
