Archive-663/nishiKodak/Canon RF/STL/nishiKodak_canonRF_mountFlange.stl

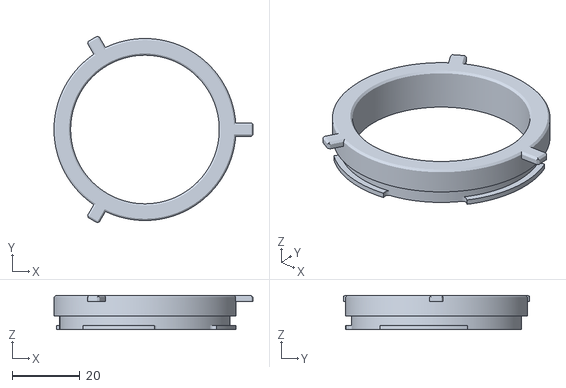
[picture p107: CAD file, 2023-11-06]
Canon RF/STL/nishiKodak_canonRF_mountFlange.stl
58.9 x 55.2 x 10.1
