Archive-663/nishiKodak/Fuji GFX/STL/nishiKodak_GFX_printOrientation.3mf

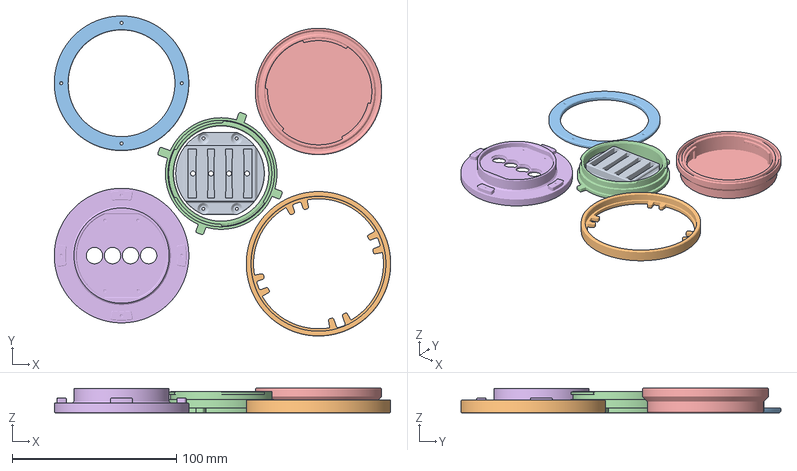
[picture p108: CAD file, 2025-04-08]
Fuji GFX/STL/nishiKodak_GFX_printOrientation.3mf
205.0 x 195.0 x 15.2 mm
nishiKodak_GFX_lensBaffle_short.stl
nishiKodak_GFX_mountLockRing.stl
nishiKodak_GFX_mountCap.stl
nishiKodak_GFX_mountFlange.stl
mountRearCapGFX.stl
nishiKodak_GFX_mainBody.stl
