Archive-663/nishiKodak/Fuji X/STL/nishiKodak_fujiX_lensBaffle_short.stl

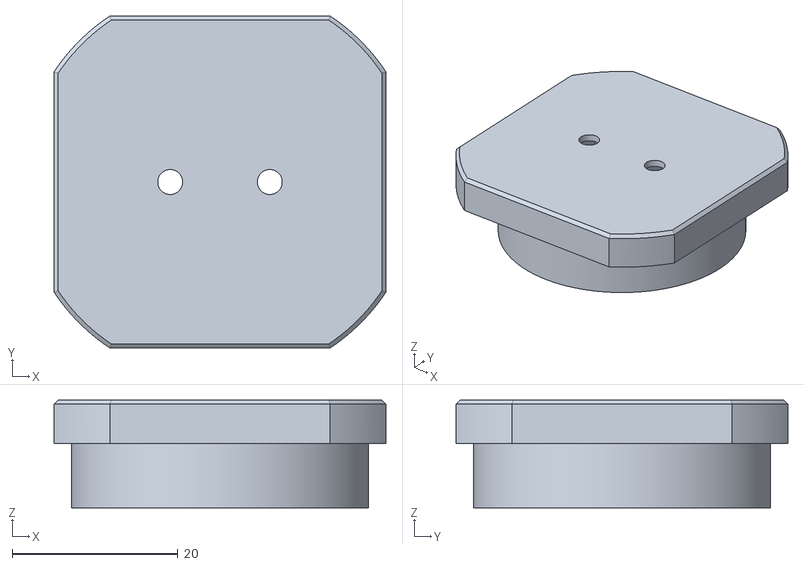
[picture p109: CAD file, 2023-11-06]
Fuji X/STL/nishiKodak_fujiX_lensBaffle_short.stl
40.0 x 40.0 x 13.0
