Archive-663/nishiKodak/Leica M/STL/nishiKodak_leicaM_mountFlange.stl

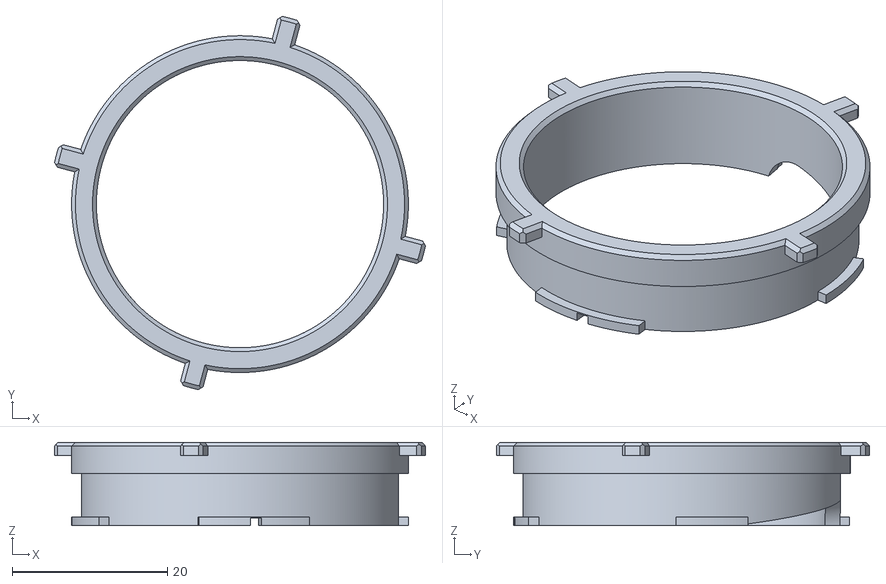
[picture p110: CAD file, 2023-11-06]
Leica M/STL/nishiKodak_leicaM_mountFlange.stl
47.8 x 48.1 x 10.8
