Archive-663/nishiKodak/Nikon Z FX/STL/nishiKodak_nikonZ_mountLockRing.stl

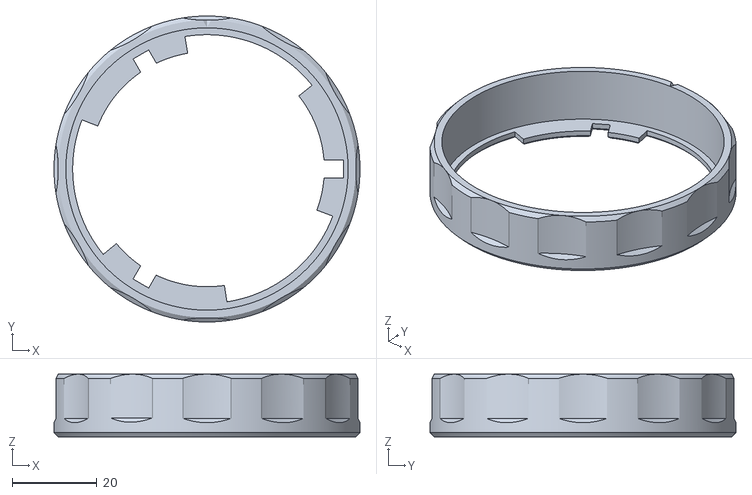
[picture p111: CAD file, 2023-11-06]
Nikon Z FX/STL/nishiKodak_nikonZ_mountLockRing.stl
72.0 x 72.0 x 14.8
