Archive-663/nishiKodak/Sony E/STL/nishiKodak_sonyFE_mountLockRing.stl

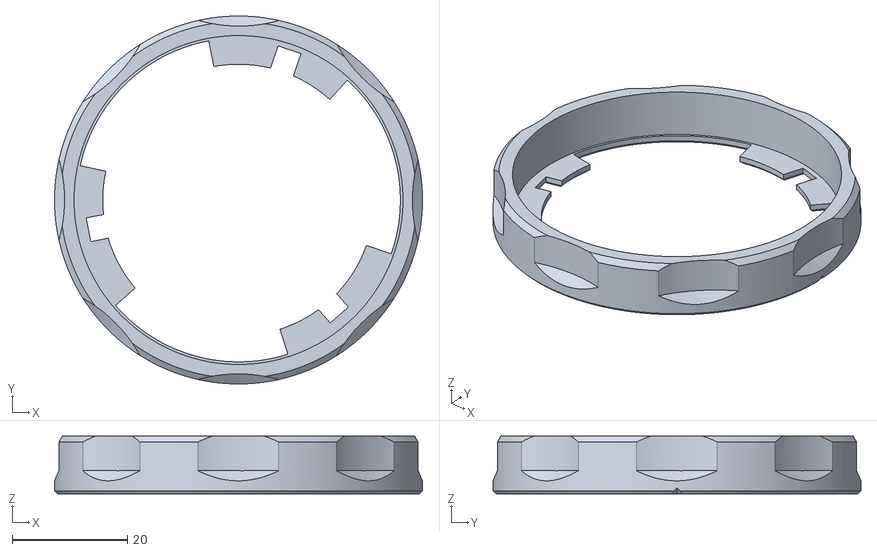
[picture p112: CAD file, 2023-11-06]
Sony E/STL/nishiKodak_sonyFE_mountLockRing.stl
64.0 x 64.0 x 10.0
