Archive-663/nishiKodak/Sony FE/STL/nishiKodak_sonyFE_mountFlange.stl

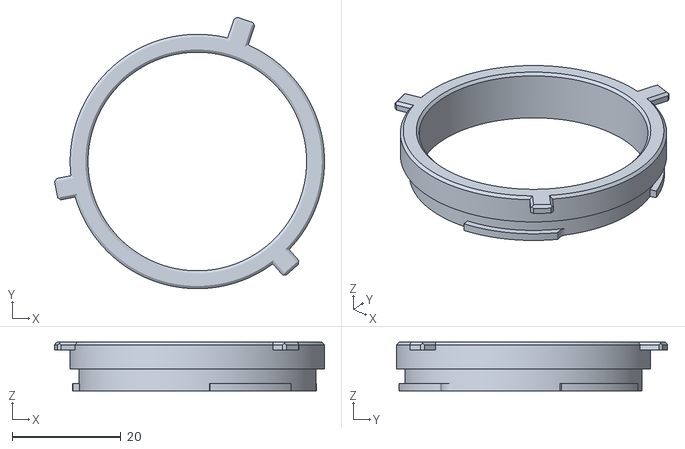
[picture p113: CAD file, 2023-11-06]
Sony FE/STL/nishiKodak_sonyFE_mountFlange.stl
49.7 x 49.9 x 9.00
