Archive-663/nishiKodak/Canon RF/STL/nishiKodak_canonRF_mountCap.stl

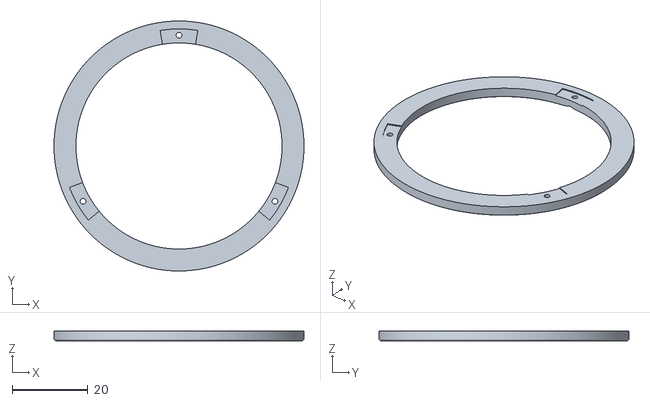
[picture p114: CAD file, 2023-11-06]
Canon RF/STL/nishiKodak_canonRF_mountCap.stl
66.0 x 66.0 x 2.75
