Archive-663/nishiKodak/Fuji GFX/STEP/nishiKodak-fujiGFX_mountFlange.stp

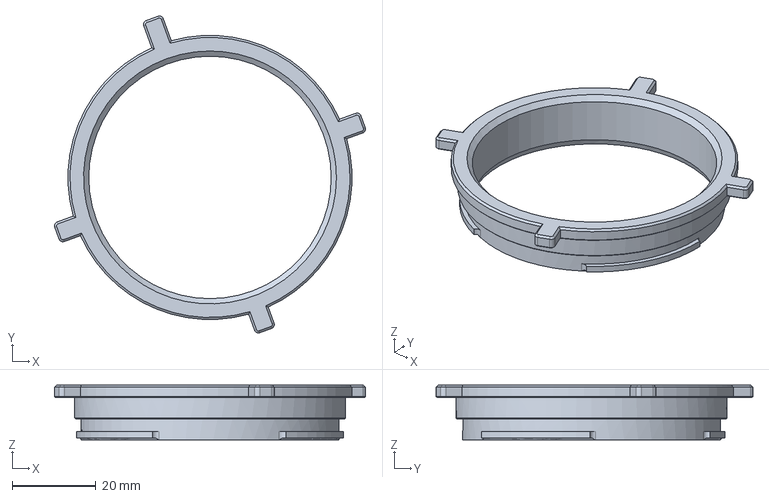
[picture p115: CAD file, 2025-04-08]
Fuji GFX/STEP/nishiKodak-fujiGFX_mountFlange.stp
74.4 x 75.9 x 13.2 mm
