Archive-663/nishiKodak/Fuji X/STL/nishiKodak_fujiX_rearCap.stl

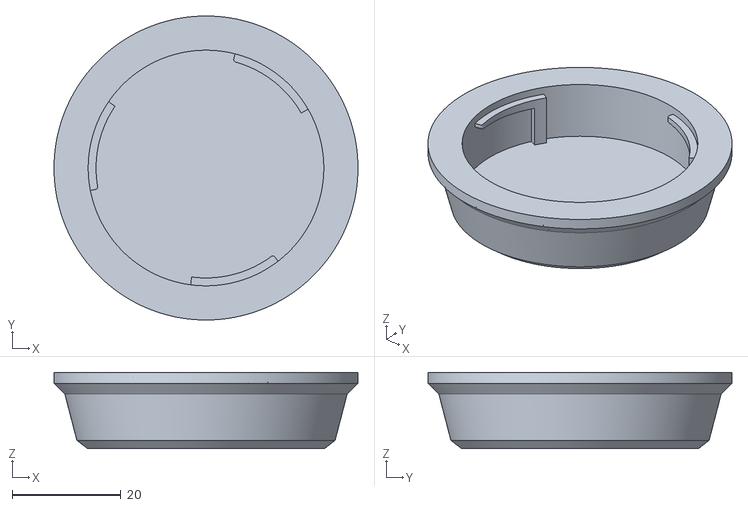
[picture p116: CAD file, 2023-11-06]
Fuji X/STL/nishiKodak_fujiX_rearCap.stl
56.0 x 56.0 x 14.0
