Archive-663/nishiKodak/Leica M/STL/nishiKodak_leicaM_bodyCap.stl

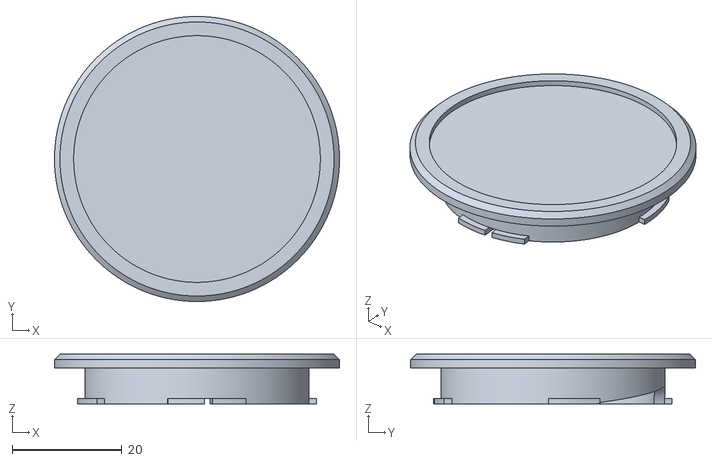
[picture p117: CAD file, 2023-11-06]
Leica M/STL/nishiKodak_leicaM_bodyCap.stl
52.0 x 52.0 x 9.05
