Archive-663/nishiKodak/Nikon Z FX/STL/nishiKodak_nikonZ_lensBody.stl

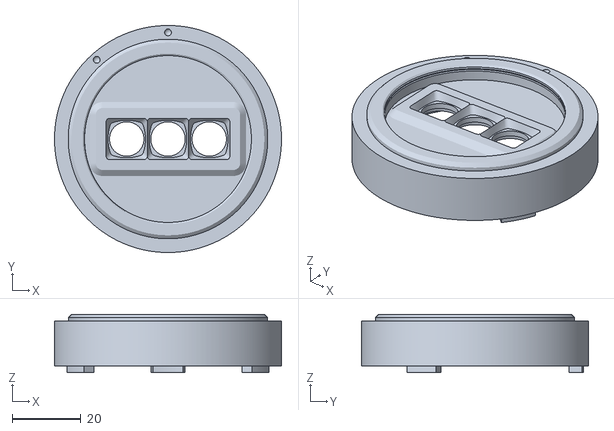
[picture p118: CAD file, 2023-11-06]
Nikon Z FX/STL/nishiKodak_nikonZ_lensBody.stl
66.0 x 66.0 x 17.0
