Archive-663/nishiKodak/Canon RF/STL/nishiKodak_canonRF_lensBaffle_long.stl

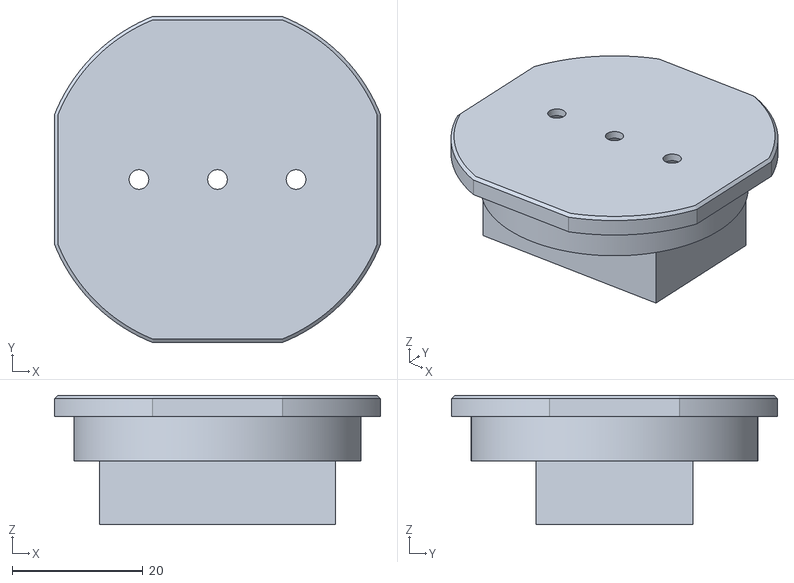
[picture p119: CAD file, 2023-11-06]
Canon RF/STL/nishiKodak_canonRF_lensBaffle_long.stl
49.8 x 49.8 x 19.8
