Archive-663/nishiKodak/Fuji X/STL/nishiKodak_fujiX_lensBaffle_long.stl

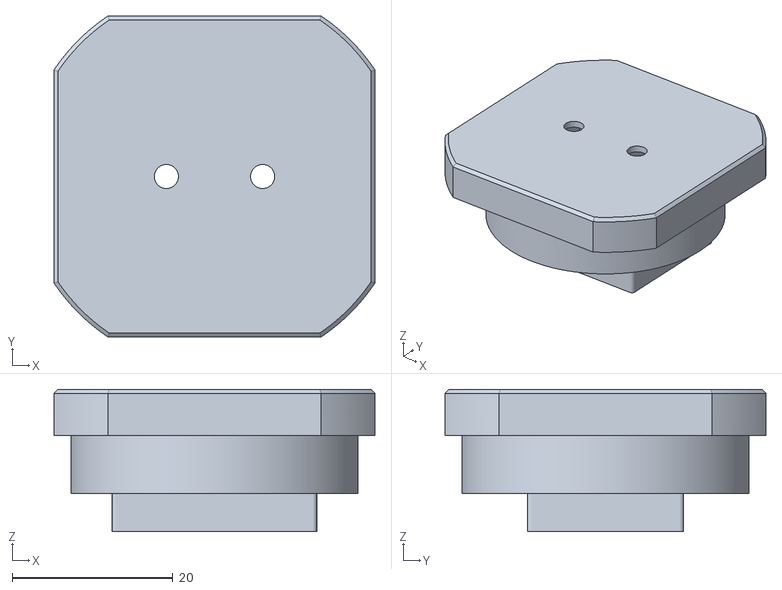
[picture p120: CAD file, 2023-11-06]
Fuji X/STL/nishiKodak_fujiX_lensBaffle_long.stl
40.0 x 40.0 x 17.8
