Archive-663/nishiKodak/Leica M/STL/nishiKodak_leicaM_mountCap.stl

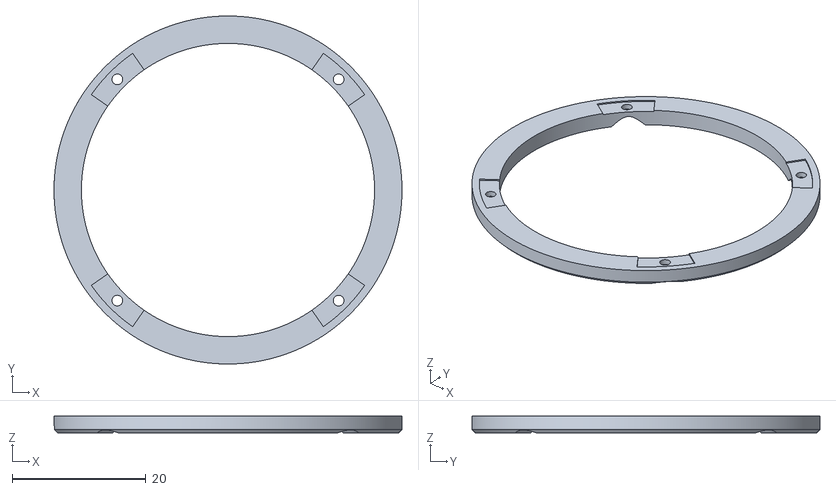
[picture p121: CAD file, 2023-11-06]
Leica M/STL/nishiKodak_leicaM_mountCap.stl
52.0 x 52.0 x 2.50
