Archive-663/nishiKodak/Sony E/STL/nishiKodak_sonyE_lensBaffle_short.stl

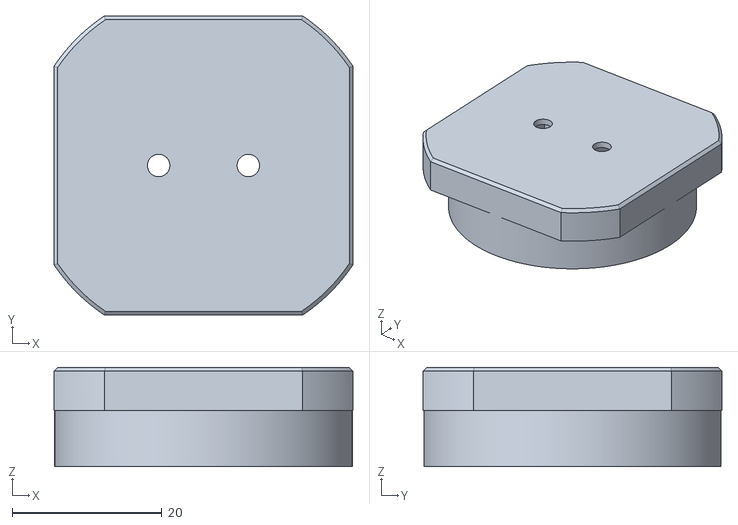
[picture p122: CAD file, 2023-11-06]
Sony E/STL/nishiKodak_sonyE_lensBaffle_short.stl
40.0 x 40.0 x 13.2
