Archive-663/nishiKodak/Leica M/STL/nishiKodak_leicaM_bodyCap_nameplate.stl

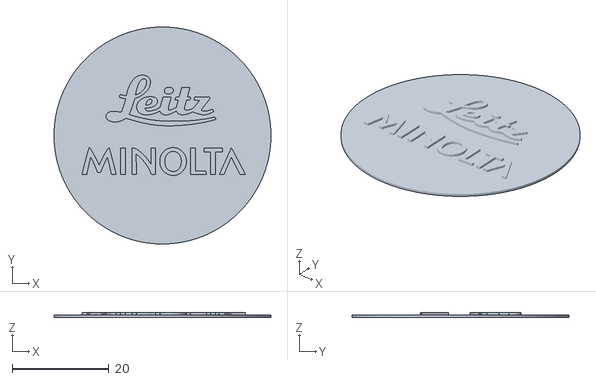
[picture p123: CAD file, 2023-11-06]
Leica M/STL/nishiKodak_leicaM_bodyCap_nameplate.stl
44.9 x 44.9 x 1.00
