Archive-663/nishiKodak/Leica M/STL/nishiKodak_leicaM_lensBaffle_short.stl

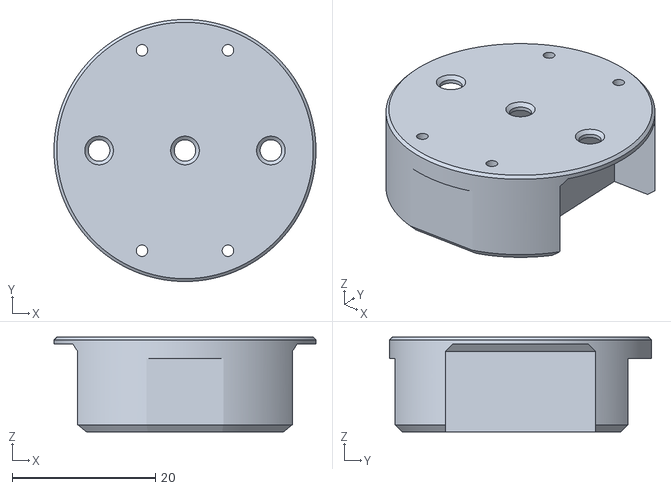
[picture p124: CAD file, 2023-11-06]
Leica M/STL/nishiKodak_leicaM_lensBaffle_short.stl
36.6 x 36.6 x 13.2
